karye/6502.smutje.se/KiCad/6502.smutje.se.kicad_sch

## KiCad design KiCad/6502.smutje.se.kicad_sch (2026-08-07, an earlier design)

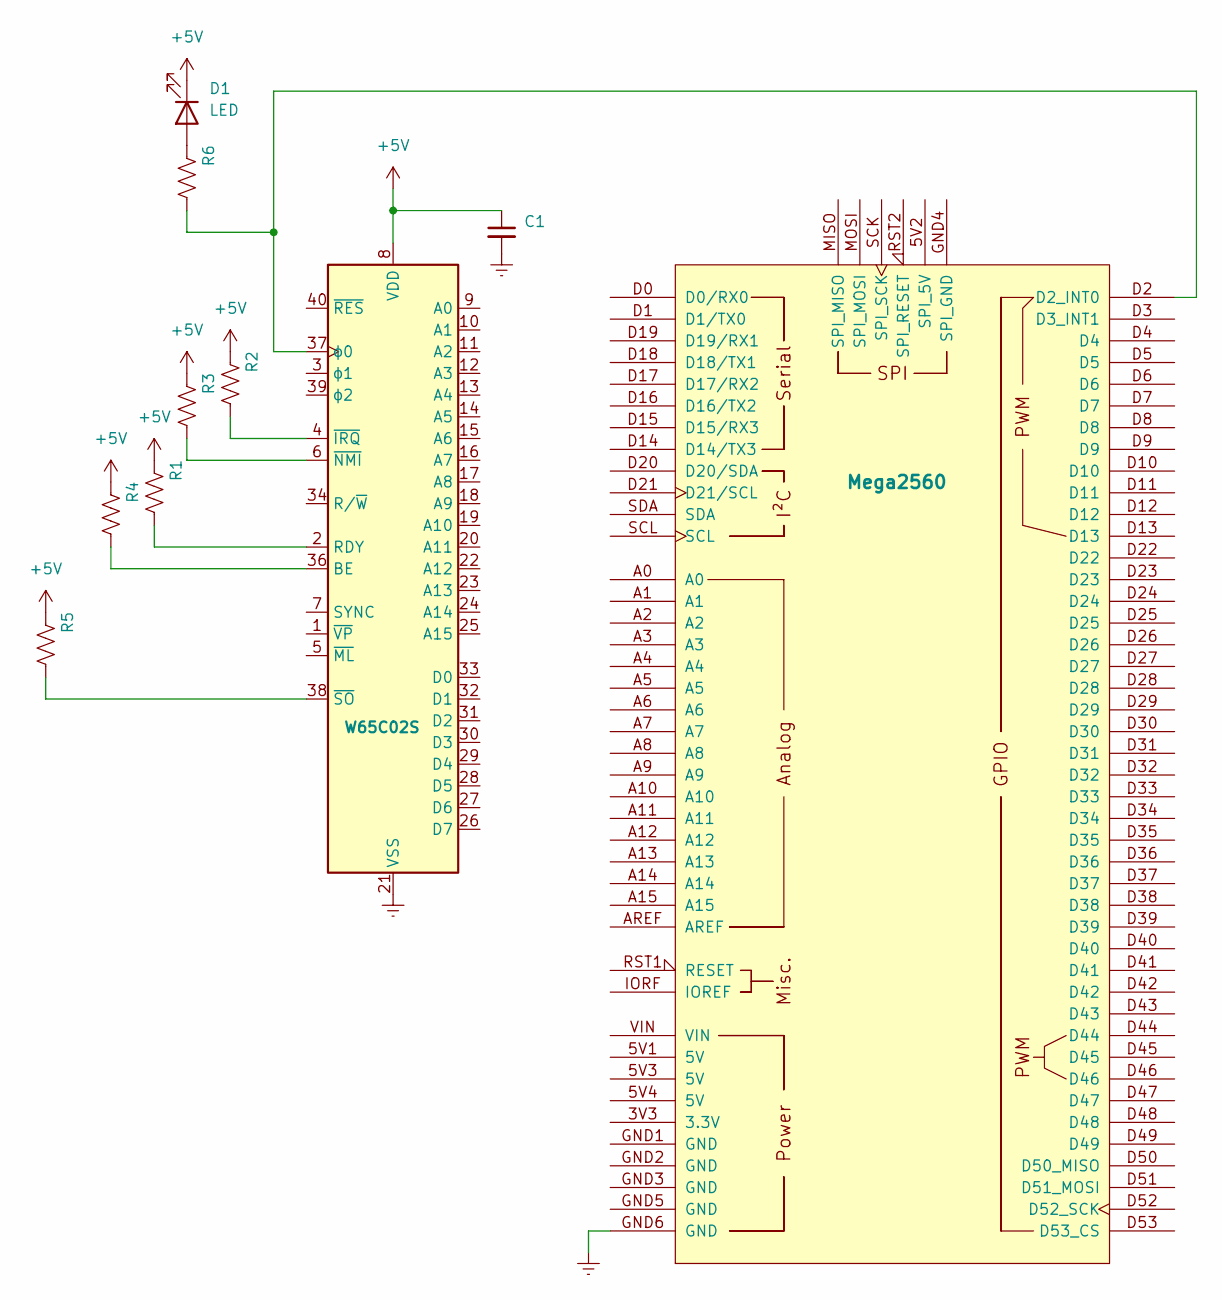
[picture p14: schematic 6502.smutje.se.kicad_sch]

Parts:
A5: Mega2560; Arduino_Mega2560_R3_Shield
C1: 100nF
D1: LED
R1, R2, R3, R4, R5: 1k
R6: 220
U11: W65C02S; DIP-40_W15.24mm

Connections:
+5V: C1.1, D1.1 (K), R1.1, R2.1, R3.1, R4.1, R5.1, U11.8 (VDD)
Earth: A5.GND6 (GND), C1.2, U11.21 (VSS)
unnamed: A5.D2 (D2_INT0), R6.2, U11.37 (ϕ0)
unnamed: D1.2 (A), R6.1
unnamed: R1.2, U11.2 (RDY)
unnamed: R2.2, U11.4 (~IRQ)
unnamed: R3.2, U11.6 (~NMI)
unnamed: R4.2, U11.36 (BE)
unnamed: R5.2, U11.38 (~SO)
