karye/6502.smutje.se/KiCad/steg_3.kicad_sch

## KiCad design KiCad/steg_3.kicad_sch (2026-08-07, an earlier design)

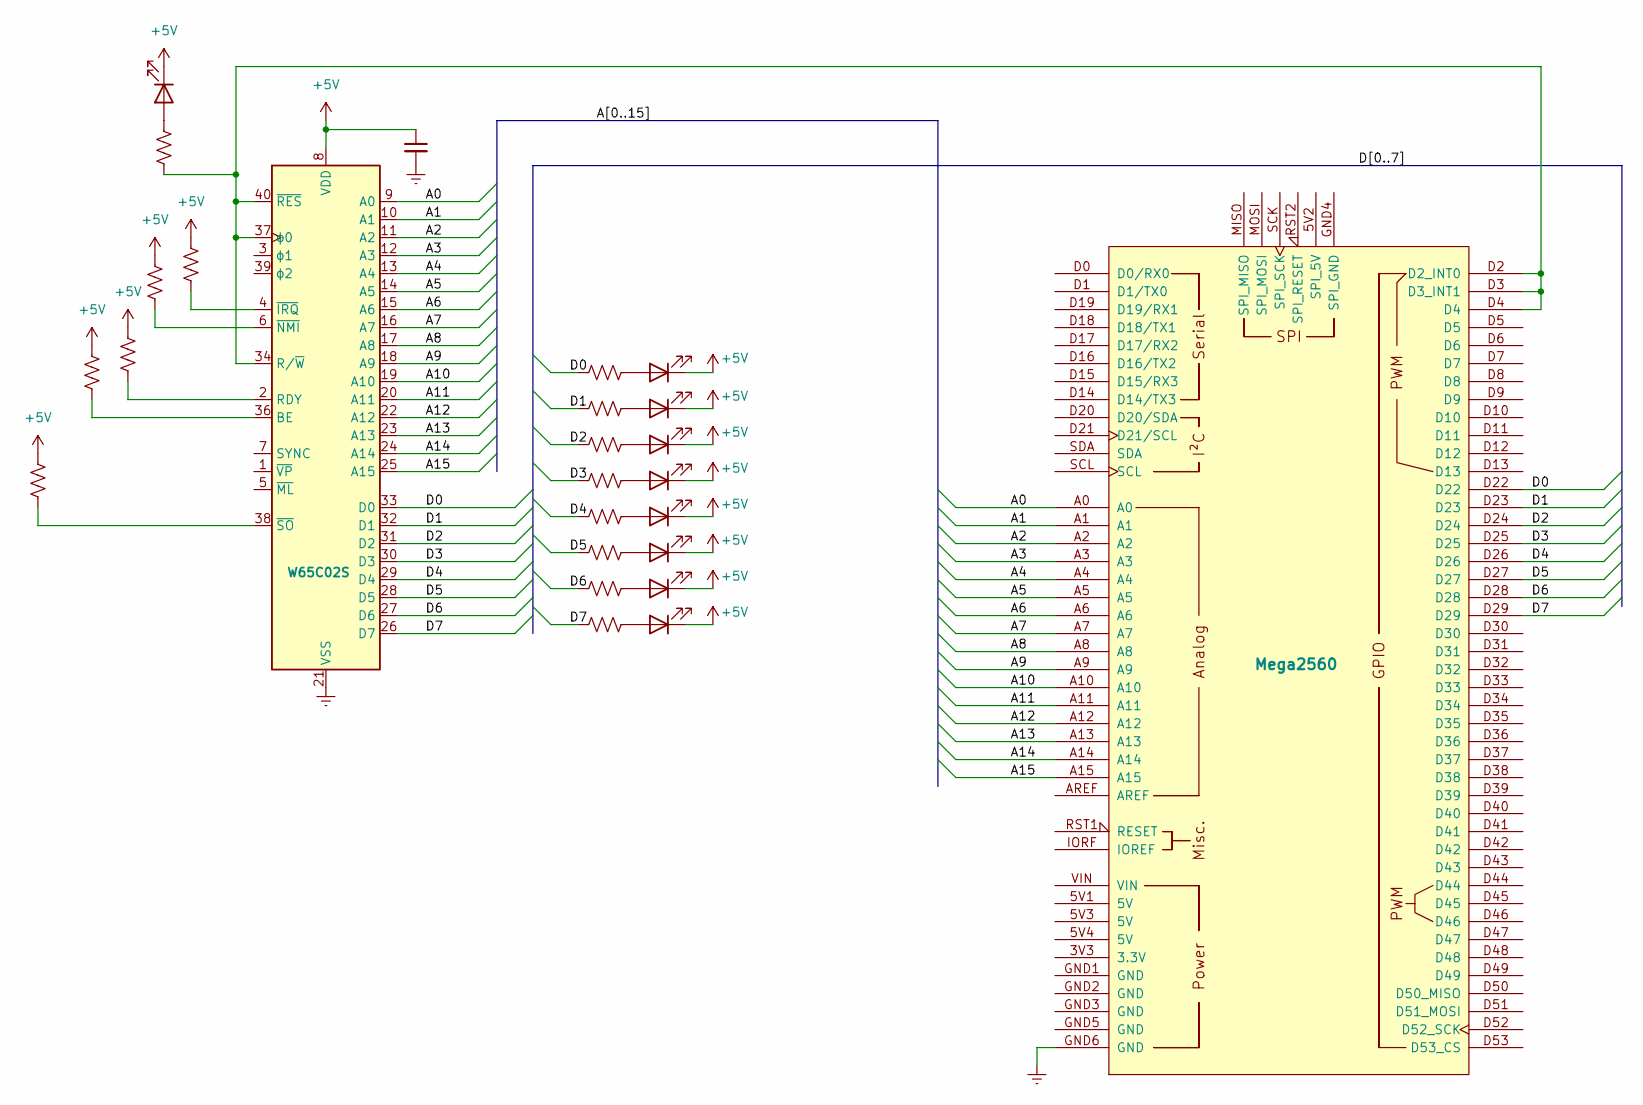
[picture p16: schematic steg_3.kicad_sch]

Parts:
A7: Mega2560; Arduino_Mega2560_R3_Shield
C3: 100nF
D3, D4, D5, D6, D7, D8, D9, D10, D11: LED
R35, R36, R37, R38, R39: (no value)
R40, R41, R42, R43, R44, R45, R46, R47, R48: 220
U13: W65C02S; DIP-40_W15.24mm

Connections:
+5V: C3.1, D3.1 (K), D4.1 (K), D5.1 (K), D6.1 (K), D7.1 (K), D8.1 (K), D9.1 (K), D10.1 (K), D11.1 (K), R35.1, R36.1, R37.1, R38.1, R39.1, U13.8 (VDD)
A0: A7.A0, U13.9 (A0)
A1: A7.A1, U13.10 (A1)
A2: A7.A2, U13.11 (A2)
A3: A7.A3, U13.12 (A3)
A4: A7.A4, U13.13 (A4)
A5: A7.A5, U13.14 (A5)
A6: A7.A6, U13.15 (A6)
A7: A7.A7, U13.16 (A7)
A8: A7.A8, U13.17 (A8)
A9: A7.A9, U13.18 (A9)
A10: A7.A10, U13.19 (A10)
A11: A7.A11, U13.20 (A11)
A12: A7.A12, U13.22 (A12)
A13: A7.A13, U13.23 (A13)
A14: A7.A14, U13.24 (A14)
A15: A7.A15, U13.25 (A15)
D0: A7.D22, R47.2, U13.33 (D0)
D1: A7.D23, R46.2, U13.32 (D1)
D2: A7.D24, R40.2, U13.31 (D2)
D3: A7.D25, R41.2, U13.30 (D3)
D4: A7.D26, R42.2, U13.29 (D4)
D5: A7.D27, R43.2, U13.28 (D5)
D6: A7.D28, R44.2, U13.27 (D6)
D7: A7.D29, R45.2, U13.26 (D7)
Earth: A7.GND6 (GND), C3.2, U13.21 (VSS)
unnamed: A7.D2 (D2_INT0), A7.D3 (D3_INT1), A7.D4, R48.2, U13.34 (R/~W), U13.37 (ϕ0), U13.40 (~RES)
unnamed: D3.2 (A), R40.1
unnamed: D4.2 (A), R41.1
unnamed: D5.2 (A), R42.1
unnamed: D6.2 (A), R43.1
unnamed: D7.2 (A), R44.1
unnamed: D8.2 (A), R45.1
unnamed: D9.2 (A), R46.1
unnamed: D10.2 (A), R47.1
unnamed: D11.2 (A), R48.1
unnamed: R35.2, U13.38 (~SO)
unnamed: R36.2, U13.36 (BE)
unnamed: R37.2, U13.2 (RDY)
unnamed: R38.2, U13.6 (~NMI)
unnamed: R39.2, U13.4 (~IRQ)
