karye/6502.smutje.se/KiCad/steg_9.kicad_sch

## KiCad design KiCad/steg_9.kicad_sch (2026-08-12, an earlier design)

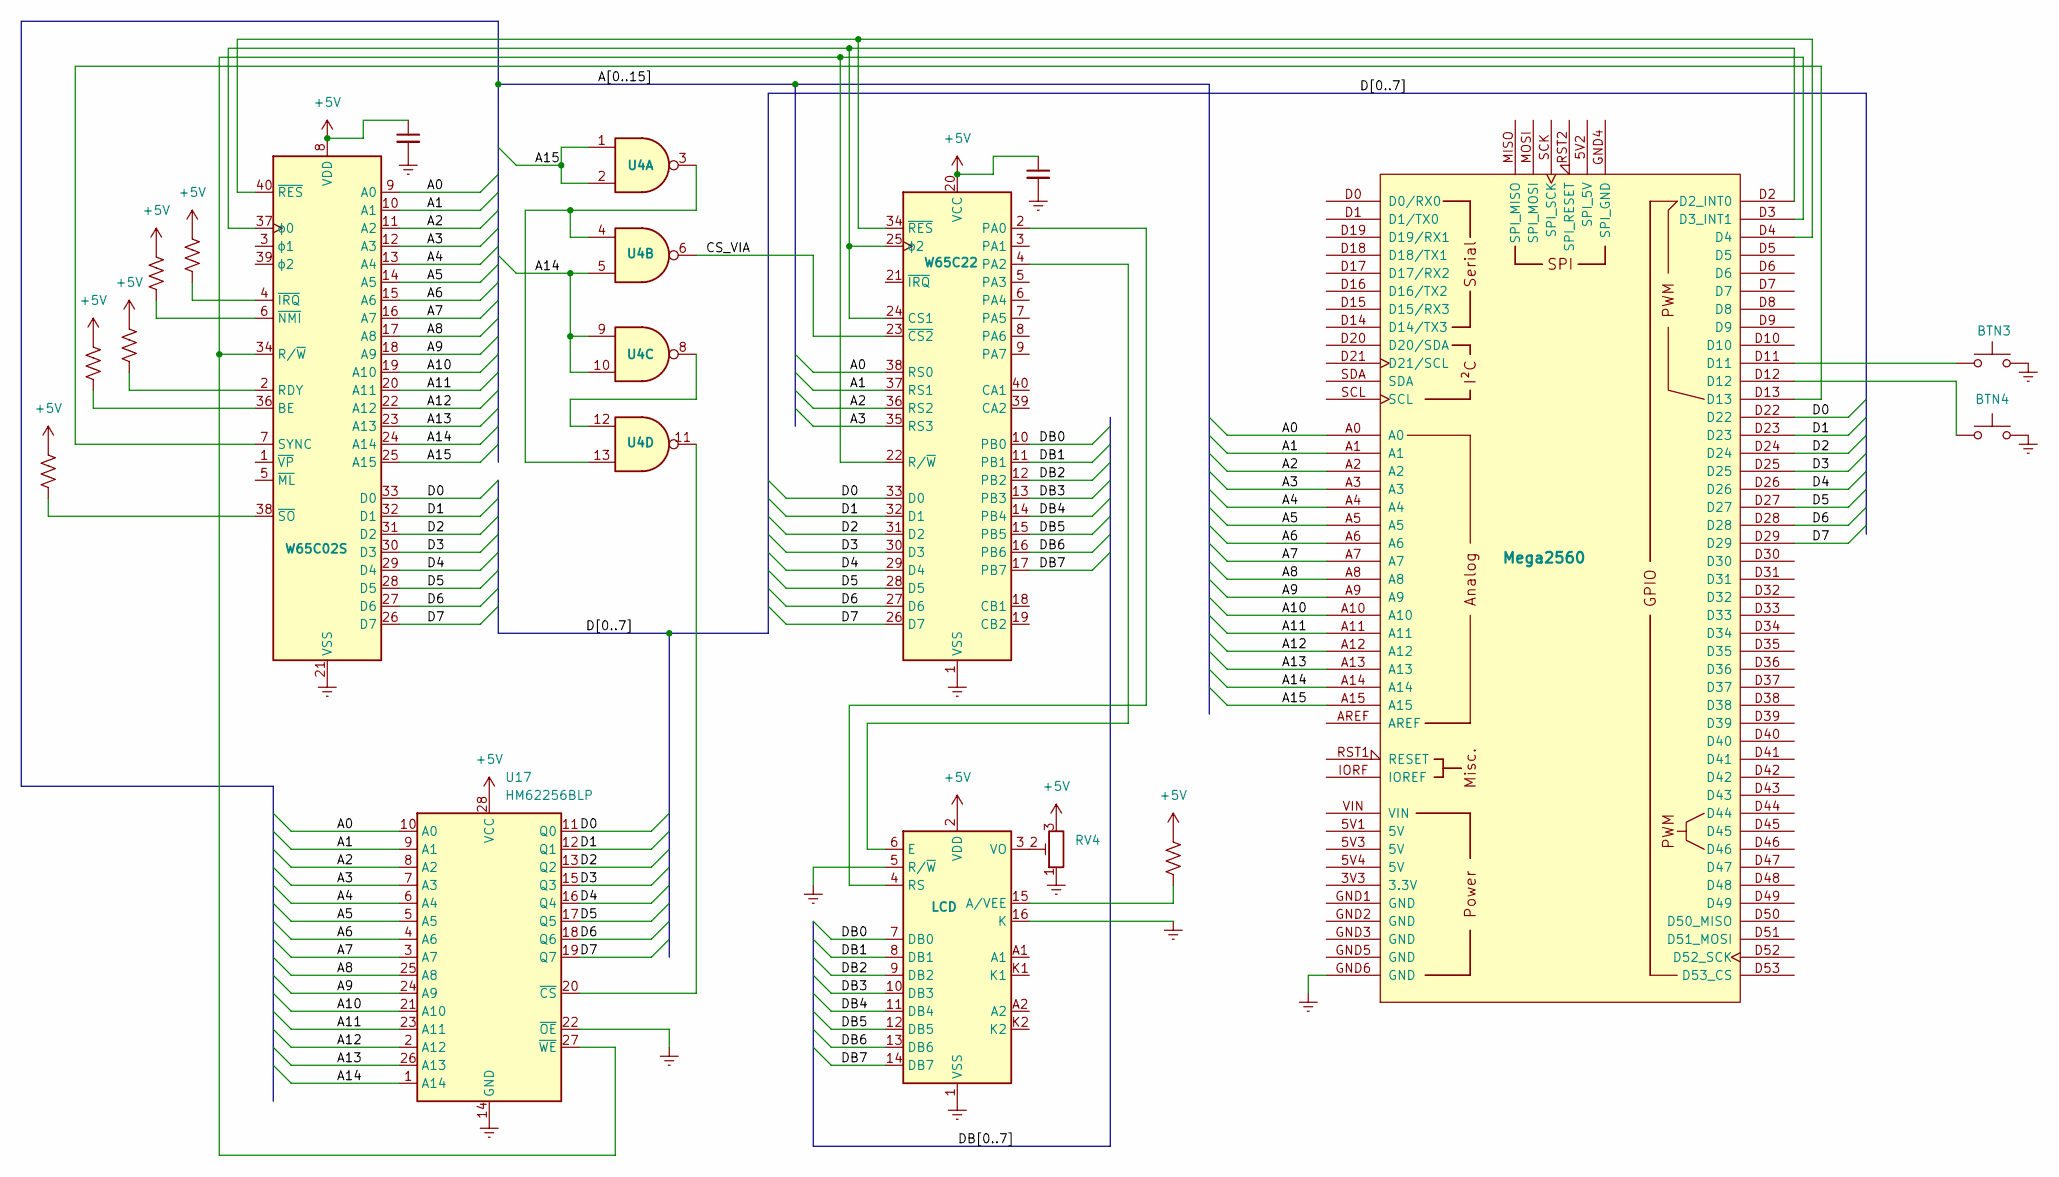
[picture p21: schematic steg_9.kicad_sch]

Parts:
A4: Mega2560; Arduino_Mega2560_R3_Shield
BTN3, BTN4: SW_Push
C9, C10: 100nF
R7, R13, R20, R22, R23: (no value)
R24: 220
RV4: R_Potentiometer_Trim
U4: 74HC00
U9: W65C02S; DIP-40_W15.24mm
U15: W65C22; DIP-40_W15.24mm
U16: LCD; LCD-016N002L
U17: HM62256BLP; DIP-28_W15.24mm

Connections:
+5V: C9.1, C10.1, R7.1, R13.1, R20.1, R22.1, R23.1, R24.1, RV4.3, U9.8 (VDD), U15.20 (VCC), U16.2 (VDD), U17.28 (VCC)
A0: A4.A0, U9.9 (A0), U15.38 (RS0), U17.10 (A0)
A1: A4.A1, U9.10 (A1), U15.37 (RS1), U17.9 (A1)
A2: A4.A2, U9.11 (A2), U15.36 (RS2), U17.8 (A2)
A3: A4.A3, U9.12 (A3), U15.35 (RS3), U17.7 (A3)
A4: A4.A4, U9.13 (A4), U17.6 (A4)
A5: A4.A5, U9.14 (A5), U17.5 (A5)
A6: A4.A6, U9.15 (A6), U17.4 (A6)
A7: A4.A7, U9.16 (A7), U17.3 (A7)
A8: A4.A8, U9.17 (A8), U17.25 (A8)
A9: A4.A9, U9.18 (A9), U17.24 (A9)
A10: A4.A10, U9.19 (A10), U17.21 (A10)
A11: A4.A11, U9.20 (A11), U17.23 (A11)
A12: A4.A12, U9.22 (A12), U17.2 (A12)
A13: A4.A13, U9.23 (A13), U17.26 (A13)
A14: A4.A14, U4.5, U4.9, U4.10, U9.24 (A14), U17.1 (A14)
A15: A4.A15, U4.1, U4.2, U9.25 (A15)
CS_VIA: U4.6, U15.23 (~CS2)
D0: A4.D22, U9.33 (D0), U15.33 (D0), U17.11 (Q0)
D1: A4.D23, U9.32 (D1), U15.32 (D1), U17.12 (Q1)
D2: A4.D24, U9.31 (D2), U15.31 (D2), U17.13 (Q2)
D3: A4.D25, U9.30 (D3), U15.30 (D3), U17.15 (Q3)
D4: A4.D26, U9.29 (D4), U15.29 (D4), U17.16 (Q4)
D5: A4.D27, U9.28 (D5), U15.28 (D5), U17.17 (Q5)
D6: A4.D28, U9.27 (D6), U15.27 (D6), U17.18 (Q6)
D7: A4.D29, U9.26 (D7), U15.26 (D7), U17.19 (Q7)
DB0: U15.10 (PB0), U16.7 (DB0)
DB1: U15.11 (PB1), U16.8 (DB1)
DB2: U15.12 (PB2), U16.9 (DB2)
DB3: U15.13 (PB3), U16.10 (DB3)
DB4: U15.14 (PB4), U16.11 (DB4)
DB5: U15.15 (PB5), U16.12 (DB5)
DB6: U15.16 (PB6), U16.13 (DB6)
DB7: U15.17 (PB7), U16.14 (DB7)
Earth: A4.GND6 (GND), BTN3.2, BTN4.2, C9.2, C10.2, RV4.1, U9.21 (VSS), U15.1 (VSS), U16.1 (VSS), U16.5 (R/~W), U16.16 (K), U17.14 (GND), U17.22 (~OE)
unnamed: A4.D2 (D2_INT0), U9.37 (ϕ0), U15.24 (CS1), U15.25 (ϕ2)
unnamed: A4.D3 (D3_INT1), U9.34 (R/~W), U15.22 (R/~W), U17.27 (~WE)
unnamed: A4.D4, U9.40 (~RES), U15.34 (~RES)
unnamed: A4.D11, BTN3.1
unnamed: A4.D12, BTN4.1
unnamed: A4.D13, U9.7 (SYNC)
unnamed: R7.2, U9.38 (~SO)
unnamed: R13.2, U9.36 (BE)
unnamed: R20.2, U9.2 (RDY)
unnamed: R22.2, U9.6 (~NMI)
unnamed: R23.2, U9.4 (~IRQ)
unnamed: R24.2, U16.15 (A/VEE)
unnamed: RV4.2, U16.3 (VO)
unnamed: U4.8, U4.12
unnamed: U4.3, U4.4, U4.13
unnamed: U15.2 (PA0), U16.4 (RS)
unnamed: U15.4 (PA2), U16.6 (E)
unnamed: U4.11, U17.20 (~CS)
