karye/6502.smutje.se/KiCad/steg_10.kicad_sch

## KiCad design KiCad/steg_10.kicad_sch (2026-08-12)

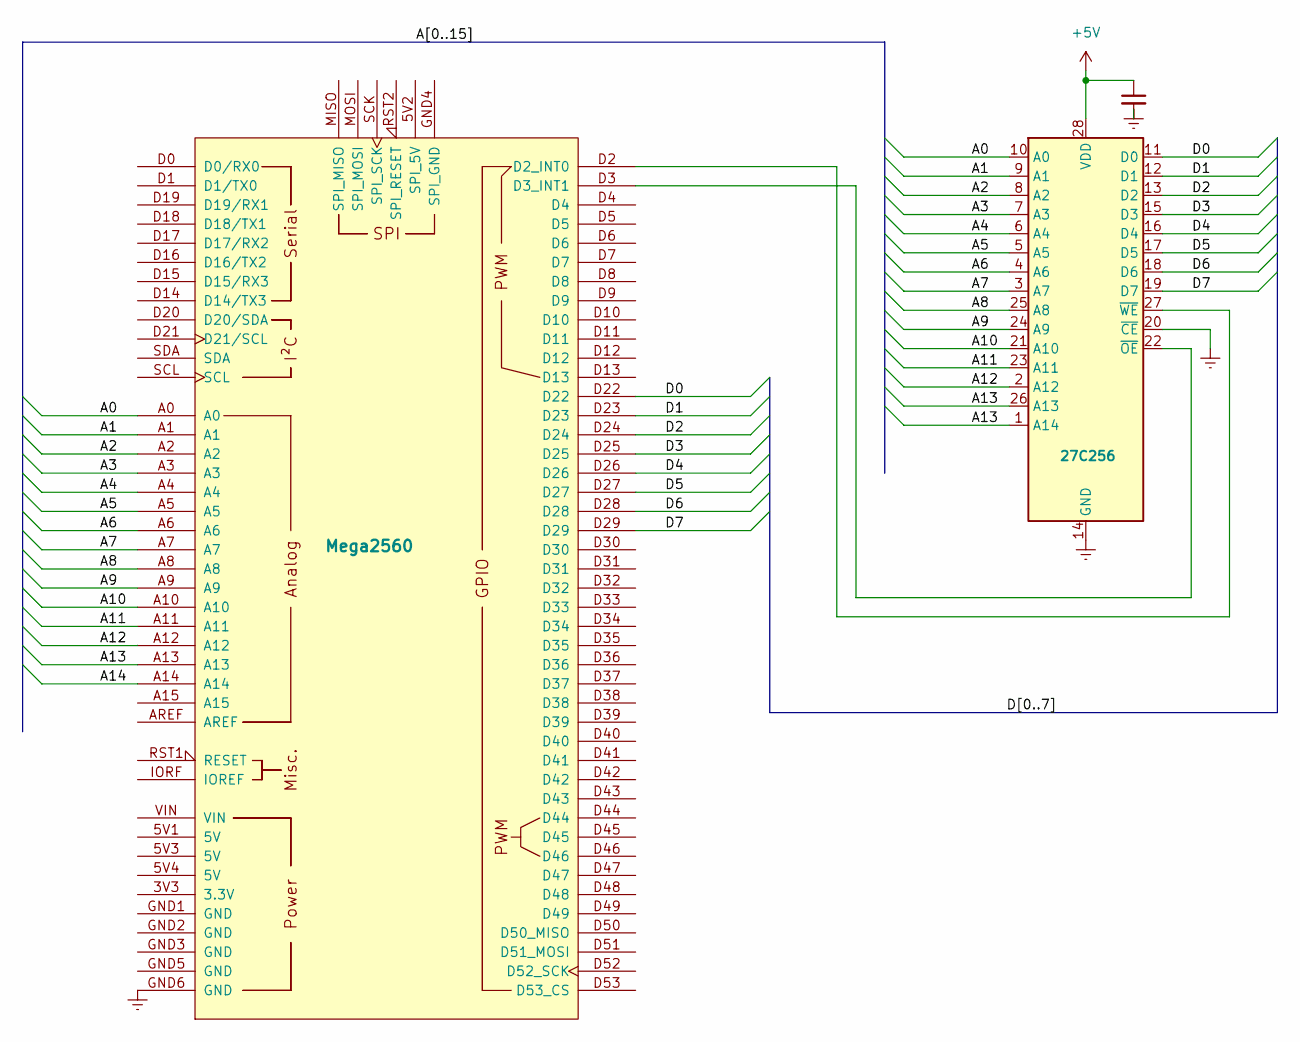
[picture p22: schematic steg_10.kicad_sch]

Parts:
A9: Mega2560; Arduino_Mega2560_R3_Shield
C11: 100nF
U10: 27C256; DIP-28_W15.24mm

Connections:
+5V: C11.1, U10.28 (VDD)
A0: A9.A0, U10.10 (A0)
A1: A9.A1, U10.9 (A1)
A2: A9.A2, U10.8 (A2)
A3: A9.A3, U10.7 (A3)
A4: A9.A4, U10.6 (A4)
A5: A9.A5, U10.5 (A5)
A6: A9.A6, U10.4 (A6)
A7: A9.A7, U10.3 (A7)
A8: A9.A8, U10.25 (A8)
A9: A9.A9, U10.24 (A9)
A10: A9.A10, U10.21 (A10)
A11: A9.A11, U10.23 (A11)
A12: A9.A12, U10.2 (A12)
A13: A9.A13, U10.1 (A14), U10.26 (A13)
A14: A9.A14
D0: A9.D22, U10.11 (D0)
D1: A9.D23, U10.12 (D1)
D2: A9.D24, U10.13 (D2)
D3: A9.D25, U10.15 (D3)
D4: A9.D26, U10.16 (D4)
D5: A9.D27, U10.17 (D5)
D6: A9.D28, U10.18 (D6)
D7: A9.D29, U10.19 (D7)
Earth: A9.GND6 (GND), C11.2, U10.14 (GND), U10.20 (~CE)
unnamed: A9.D2 (D2_INT0), U10.27 (~WE)
unnamed: A9.D3 (D3_INT1), U10.22 (~OE)
