karye/6502.smutje.se/KiCad/6502.smutje.se.steg-7/6502.smutje.se.kicad_sch

## KiCad design KiCad/6502.smutje.se.steg-7/6502.smutje.se.kicad_sch (2026-08-04)

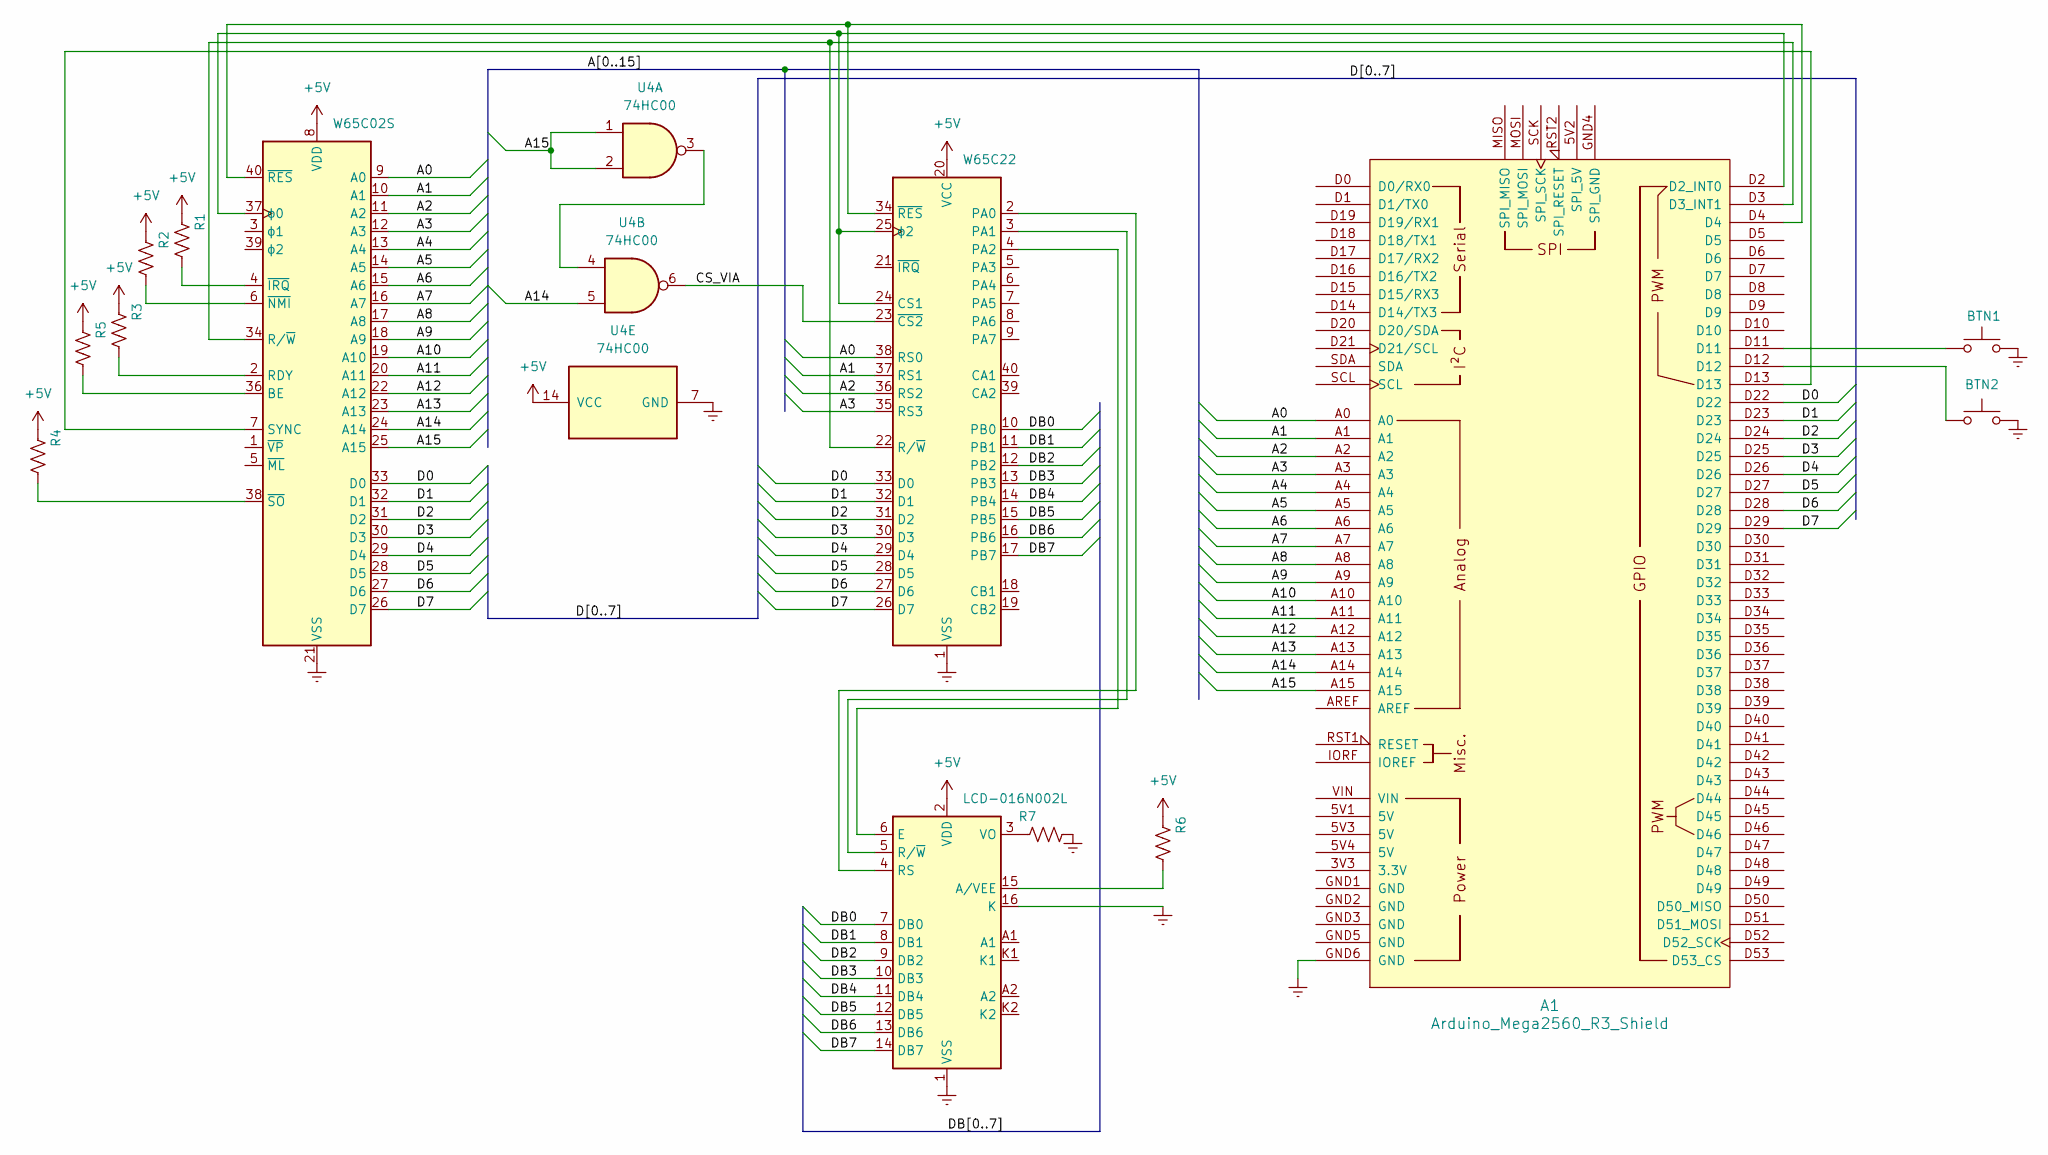
[picture p25: schematic 6502.smutje.se.kicad_sch]

Parts:
A1: Arduino_Mega2560_R3_Shield
BTN1, BTN2: SW_Push
R1, R2, R3, R4, R5, R6, R7: (no value)
U1: W65C02S; DIP-40_W15.24mm
U2: LCD-016N002L
U3: W65C22; DIP-40_W15.24mm
U4: 74HC00

Connections:
+5V: R1.1, R2.1, R3.1, R4.1, R5.1, R6.1, U1.8 (VDD), U2.2 (VDD), U3.20 (VCC), U4.14 (VCC)
A0: A1.A0, U1.9 (A0), U3.38 (RS0)
A1: A1.A1, U1.10 (A1), U3.37 (RS1)
A2: A1.A2, U1.11 (A2), U3.36 (RS2)
A3: A1.A3, U1.12 (A3), U3.35 (RS3)
A4: A1.A4, U1.13 (A4)
A5: A1.A5, U1.14 (A5)
A6: A1.A6, U1.15 (A6)
A7: A1.A7, U1.16 (A7)
A8: A1.A8, U1.17 (A8)
A9: A1.A9, U1.18 (A9)
A10: A1.A10, U1.19 (A10)
A11: A1.A11, U1.20 (A11)
A12: A1.A12, U1.22 (A12)
A13: A1.A13, U1.23 (A13)
A14: A1.A14, U1.24 (A14), U4.5
A15: A1.A15, U1.25 (A15), U4.1, U4.2
CS_VIA: U3.23 (~CS2), U4.6
D0: A1.D22, U1.33 (D0), U3.33 (D0)
D1: A1.D23, U1.32 (D1), U3.32 (D1)
D2: A1.D24, U1.31 (D2), U3.31 (D2)
D3: A1.D25, U1.30 (D3), U3.30 (D3)
D4: A1.D26, U1.29 (D4), U3.29 (D4)
D5: A1.D27, U1.28 (D5), U3.28 (D5)
D6: A1.D28, U1.27 (D6), U3.27 (D6)
D7: A1.D29, U1.26 (D7), U3.26 (D7)
DB0: U2.7 (DB0), U3.10 (PB0)
DB1: U2.8 (DB1), U3.11 (PB1)
DB2: U2.9 (DB2), U3.12 (PB2)
DB3: U2.10 (DB3), U3.13 (PB3)
DB4: U2.11 (DB4), U3.14 (PB4)
DB5: U2.12 (DB5), U3.15 (PB5)
DB6: U2.13 (DB6), U3.16 (PB6)
DB7: U2.14 (DB7), U3.17 (PB7)
Earth: A1.GND6 (GND), BTN1.2, BTN2.2, R7.2, U1.21 (VSS), U2.1 (VSS), U2.16 (K), U3.1 (VSS), U4.7 (GND)
unnamed: A1.D2 (D2_INT0), U1.37 (ϕ0), U3.24 (CS1), U3.25 (ϕ2)
unnamed: A1.D3 (D3_INT1), U1.34 (R/~W), U3.22 (R/~W)
unnamed: A1.D4, U1.40 (~RES), U3.34 (~RES)
unnamed: A1.D11, BTN1.1
unnamed: A1.D12, BTN2.1
unnamed: A1.D13, U1.7 (SYNC)
unnamed: R1.2, U1.4 (~IRQ)
unnamed: R2.2, U1.6 (~NMI)
unnamed: R3.2, U1.2 (RDY)
unnamed: R4.2, U1.38 (~SO)
unnamed: R5.2, U1.36 (BE)
unnamed: R6.2, U2.15 (A/VEE)
unnamed: R7.1, U2.3 (VO)
unnamed: U2.4 (RS), U3.2 (PA0)
unnamed: U2.5 (R/~W), U3.3 (PA1)
unnamed: U2.6 (E), U3.4 (PA2)
unnamed: U4.3, U4.4
