karye/6502.smutje.se/Mega_2560_6502/src/program_fib.h

// Genererad från program.bin — redigera inte för hand
// Storlek: 2054 bytes

#include <avr/pgmspace.h>

const unsigned char PROGRAM_FIB[] PROGMEM = {
    0xA9, 0xFF, 0x8D, 0x02, 0x40, 0x8D, 0x03, 0x40, 0xA9, 0x30, 0x20, 0xE1, 0x80, 0xA9, 0x30, 0x20,
    0xE1, 0x80, 0xA9, 0x30, 0x20, 0xE1, 0x80, 0xA9, 0x38, 0x20, 0xE1, 0x80, 0xA9, 0x0C, 0x20, 0xE1,
    0x80, 0xA9, 0x01, 0x20, 0xE1, 0x80, 0xA9, 0x06, 0x20, 0xE1, 0x80, 0xA9, 0x80, 0x20, 0xE1, 0x80,
    0xA9, 0x01, 0x8D, 0x01, 0x40, 0xA2, 0x00, 0xBD, 0xFD, 0x80, 0xF0, 0x07, 0x20, 0xEF, 0x80, 0xE8,
    0x4C, 0x37, 0x80, 0xA9, 0x00, 0x85, 0x00, 0xA9, 0x01, 0x85, 0x01, 0xA9, 0x00, 0x20, 0x8B, 0x80,
    0x20, 0x80, 0x80, 0xA9, 0x01, 0x20, 0x8B, 0x80, 0x20, 0x80, 0x80, 0x18, 0xA5, 0x00, 0x65, 0x01,
    0x90, 0x0B, 0xA9, 0x00, 0x85, 0x00, 0xA9, 0x01, 0x85, 0x01, 0x4C, 0x5B, 0x80, 0x85, 0x02, 0xA5,
    0x01, 0x85, 0x00, 0xA5, 0x02, 0x85, 0x01, 0x20, 0x8B, 0x80, 0x20, 0x80, 0x80, 0x4C, 0x5B, 0x80,
    0xA2, 0x05, 0xA0, 0x05, 0x88, 0xD0, 0xFD, 0xCA, 0xD0, 0xF8, 0x60, 0x85, 0x10, 0xA9, 0xC0, 0x20,
    0xE1, 0x80, 0xA9, 0x01, 0x8D, 0x01, 0x40, 0xA5, 0x10, 0xA2, 0x00, 0xC9, 0x64, 0x90, 0x07, 0xE8,
    0x38, 0xE9, 0x64, 0x4C, 0x9B, 0x80, 0x48, 0x8A, 0xF0, 0x06, 0x18, 0x69, 0x30, 0x20, 0xEF, 0x80,
    0x68, 0xA2, 0x00, 0xC9, 0x0A, 0x90, 0x07, 0xE8, 0x38, 0xE9, 0x0A, 0x4C, 0xB3, 0x80, 0x48, 0x8A,
    0xD0, 0x06, 0xA5, 0x10, 0xC9, 0x0A, 0x90, 0x07, 0x8A, 0x18, 0x69, 0x30, 0x20, 0xEF, 0x80, 0x68,
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
    0x00, 0x00, 0x00, 0x00, 0x00, 0x00, 0x00, 0x00, 0x00, 0x00, 0x00, 0x00, 0x00, 0x00, 0x00, 0x00,
    0x00, 0x00, 0x00, 0x00, 0x00, 0x00, 0x00, 0x00, 0x00, 0x00, 0x00, 0x00, 0x00, 0x00, 0x00, 0x00,
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
};
const unsigned int PROGRAM_FIB_SIZE = 2054;
