karye/6502.smutje.se/Mega_2560_6502/src/program_hello.h

// Genererad från program.bin — redigera inte för hand
// Storlek: 2054 bytes

#include <avr/pgmspace.h>

const unsigned char PROGRAM[] PROGMEM = {
    0xA9, 0xFF, 0x8D, 0x02, 0x40, 0x8D, 0x03, 0x40, 0xA9, 0x30, 0x20, 0x93, 0x80, 0xA9, 0x30, 0x20,
    0x93, 0x80, 0xA9, 0x30, 0x20, 0x93, 0x80, 0xA9, 0x38, 0x20, 0x93, 0x80, 0xA9, 0x0C, 0x20, 0x93,
    0x80, 0xA9, 0x01, 0x20, 0x93, 0x80, 0xA9, 0x06, 0x20, 0x93, 0x80, 0xA9, 0x80, 0x20, 0x93, 0x80,
    0xA9, 0x01, 0x8D, 0x01, 0x40, 0xA2, 0x00, 0xBD, 0xAF, 0x80, 0xF0, 0x07, 0x20, 0xA1, 0x80, 0xE8,
    0x4C, 0x37, 0x80, 0xA9, 0xC0, 0x20, 0x93, 0x80, 0xA9, 0x01, 0x8D, 0x01, 0x40, 0xA2, 0x00, 0xBD,
    0xC4, 0x80, 0xF0, 0x07, 0x20, 0xA1, 0x80, 0xE8, 0x4C, 0x4F, 0x80, 0xA9, 0x94, 0x20, 0x93, 0x80,
    0xA9, 0x01, 0x8D, 0x01, 0x40, 0xA2, 0x00, 0xBD, 0xD7, 0x80, 0xF0, 0x07, 0x20, 0xA1, 0x80, 0xE8,
    0x4C, 0x67, 0x80, 0xA9, 0xD4, 0x20, 0x93, 0x80, 0xA9, 0x01, 0x8D, 0x01, 0x40, 0xA2, 0x00, 0xBD,
    0xEB, 0x80, 0xF0, 0x07, 0x20, 0xA1, 0x80, 0xE8, 0x4C, 0x7F, 0x80, 0xA9, 0x01, 0x20, 0x93, 0x80,
    0x4C, 0x2B, 0x80, 0x8D, 0x00, 0x40, 0xA9, 0x04, 0x8D, 0x01, 0x40, 0xA9, 0x00, 0x8D, 0x01, 0x40,
    0x60, 0x8D, 0x00, 0x40, 0xA9, 0x05, 0x8D, 0x01, 0x40, 0xA9, 0x01, 0x8D, 0x01, 0x40, 0x60, 0x3D,
    0x3D, 0x3D, 0x20, 0x36, 0x35, 0x30, 0x32, 0x20, 0x56, 0x49, 0x41, 0x20, 0x4C, 0x43, 0x44, 0x20,
    0x3D, 0x3D, 0x3D, 0x00, 0x48, 0x65, 0x6C, 0x6C, 0x6F, 0x20, 0x66, 0x72, 0x6F, 0x6D, 0x20, 0x57,
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
    0x00, 0x00, 0x00, 0x00, 0x00, 0x00, 0x00, 0x00, 0x00, 0x00, 0x00, 0x00, 0x00, 0x00, 0x00, 0x00,
    0x00, 0x00, 0x00, 0x00, 0x00, 0x00, 0x00, 0x00, 0x00, 0x00, 0x00, 0x00, 0x00, 0x00, 0x00, 0x00,
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
};
const unsigned int PROGRAM_SIZE = 2054;
